bleckers/brtro-420-better-blazin/brtro-reflow/splash-chm.h

#define splash_width 128
#define splash_height 64
static const uint8_t splash_bits[] U8X8_PROGMEM  = {
   0xff, 0xff, 0xff, 0xff, 0xff, 0xff, 0xff, 0xff, 0xff, 0xff, 0xff, 0xff,
   0xff, 0xff, 0xff, 0xff, 0x01, 0x00, 0x00, 0x00, 0x00, 0x00, 0x00, 0x00,
   0x00, 0x00, 0x00, 0x00, 0x00, 0x00, 0x00, 0x80, 0xfd, 0xff, 0xff, 0xff,
   0xff, 0xff, 0xff, 0xff, 0xff, 0xff, 0xff, 0xff, 0xff, 0xff, 0xff, 0xbf,
   0x05, 0x00, 0x00, 0x00, 0x00, 0x00, 0x00, 0x00, 0x00, 0x00, 0x00, 0x00,
   0x00, 0x00, 0x00, 0xa0, 0x05, 0x00, 0x00, 0x00, 0x00, 0x00, 0x00, 0x00,
   0x00, 0x00, 0x00, 0x00, 0x00, 0x00, 0x00, 0xa0, 0x05, 0x00, 0x00, 0x00,
   0x00, 0x00, 0x00, 0x00, 0x00, 0x78, 0x00, 0xf0, 0x00, 0xe0, 0x01, 0xa0,
   0x05, 0x00, 0x00, 0x00, 0x00, 0x00, 0x00, 0x00, 0x00, 0x88, 0x01, 0x10,
   0x03, 0x20, 0x06, 0xa0, 0x05, 0x00, 0x00, 0x00, 0x00, 0x00, 0x00, 0x00,
   0x00, 0x08, 0x02, 0x10, 0x04, 0x20, 0x08, 0xa0, 0x85, 0x20, 0x08, 0x20,
   0x00, 0x00, 0x00, 0x00, 0x00, 0x38, 0x04, 0x70, 0x08, 0xe0, 0x10, 0xa0,
   0x85, 0x20, 0x08, 0x20, 0x00, 0x00, 0x00, 0x00, 0x00, 0xc4, 0x08, 0x88,
   0x11, 0x10, 0x23, 0xa0, 0x85, 0x20, 0x08, 0x20, 0x00, 0x00, 0x00, 0x00,
   0x00, 0x64, 0x11, 0x38, 0x22, 0x90, 0x45, 0xa0, 0x05, 0x51, 0xc4, 0x23,
   0x1c, 0x1c, 0x9a, 0xe1, 0x01, 0x94, 0x22, 0x48, 0x44, 0x50, 0x8a, 0xa0,
   0x05, 0x51, 0x24, 0x24, 0x22, 0x22, 0x66, 0x12, 0x02, 0x94, 0x44, 0x48,
   0x88, 0x50, 0x12, 0xa1, 0x05, 0x51, 0x24, 0x24, 0x01, 0x41, 0x22, 0x12,
   0x02, 0x62, 0x48, 0x34, 0x96, 0x88, 0x21, 0xa1, 0x05, 0x8a, 0xe2, 0x27,
   0x01, 0x41, 0x22, 0xf2, 0x03, 0x02, 0x88, 0x04, 0x19, 0x09, 0x20, 0xa2,
   0x05, 0x8a, 0x22, 0x20, 0x01, 0x41, 0x22, 0x12, 0x00, 0x06, 0x93, 0x04,
   0x29, 0x19, 0x4c, 0xa2, 0x05, 0x8a, 0x22, 0x20, 0x01, 0x41, 0x22, 0x12,
   0x00, 0x8a, 0x94, 0x04, 0x26, 0x29, 0x52, 0xa2, 0x05, 0x04, 0x21, 0x24,
   0x22, 0x22, 0x22, 0x12, 0x02, 0x89, 0xf4, 0x32, 0xe0, 0x25, 0xd2, 0xa3,
   0x05, 0x04, 0xc1, 0x23, 0x1c, 0x1c, 0x22, 0xe2, 0x01, 0x07, 0x0f, 0x4a,
   0x1e, 0x1c, 0x3c, 0xa0, 0x05, 0x00, 0x00, 0x00, 0x00, 0x00, 0x00, 0x00,
   0x00, 0xf1, 0x00, 0xea, 0x01, 0xc4, 0x03, 0xa0, 0x05, 0x00, 0x00, 0x00,
   0x00, 0x00, 0x00, 0x00, 0x00, 0x0f, 0x00, 0x1e, 0x00, 0x3c, 0x00, 0xa0,
   0x05, 0x00, 0x00, 0x00, 0x00, 0x00, 0x00, 0x00, 0x00, 0x00, 0x00, 0x00,
   0x00, 0x00, 0x00, 0xa0, 0x05, 0x00, 0x00, 0x00, 0x00, 0x00, 0x00, 0x00,
   0x00, 0x00, 0x00, 0x00, 0x00, 0x00, 0x00, 0xa0, 0xfd, 0xff, 0xff, 0xff,
   0xff, 0xff, 0xff, 0xff, 0xff, 0xff, 0xff, 0xff, 0xff, 0xff, 0xff, 0xbf,
   0xfd, 0xff, 0xff, 0xff, 0xff, 0xff, 0xff, 0xff, 0xff, 0xff, 0xff, 0xff,
   0xff, 0xff, 0xff, 0xbf, 0xfd, 0xff, 0xff, 0xff, 0xff, 0xff, 0xff, 0xff,
   0xff, 0xff, 0xff, 0xff, 0xff, 0xff, 0xff, 0xbf, 0xfd, 0xff, 0x87, 0xf7,
   0xb7, 0xbf, 0x01, 0x7f, 0xf0, 0xff, 0xff, 0x7c, 0xf8, 0xe1, 0xff, 0xbf,
   0xfd, 0xff, 0x7b, 0xf7, 0x37, 0x9f, 0xfd, 0xbe, 0xef, 0xff, 0x7f, 0xbd,
   0xf7, 0xde, 0xff, 0xbf, 0xfd, 0xff, 0xfd, 0xf6, 0xb7, 0xae, 0xfd, 0xdd,
   0xdf, 0xff, 0x7f, 0xdd, 0x6f, 0xbf, 0xff, 0xbf, 0xfd, 0xff, 0xfd, 0xf7,
   0xb7, 0xb5, 0xfd, 0xdd, 0xdf, 0xff, 0xbf, 0xdd, 0x6f, 0xbf, 0xff, 0xbf,
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
