bleckers/brtro-420-better-blazin/brtro-reflow/history_buffer.h

/**
   MappyDot Firmware - history_buffer.h

   Copyright (C) 2017 SensorDots.org

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
*/


#ifndef BUFFER_H_
#define BUFFER_H_

#ifdef __cplusplus
extern "C" {
#endif

#include <stddef.h>
#include <stdint.h>


typedef struct circular_history_buffer
{
    void *buffer;     // data buffer
    void *buffer_end; // end of data buffer
    size_t capacity;  // maximum number of items in the buffer
    size_t count;     // number of items in the buffer
    size_t sz;        // size of each item in the buffer
    void *head;       // pointer to head
    void *tail;       // pointer to tail
} circular_history_buffer;

void hb_init(circular_history_buffer *cb, size_t capacity, size_t sz);

void hb_free(circular_history_buffer *cb);

void hb_push_back(circular_history_buffer *cb, const void *item);

void hb_pop_front(circular_history_buffer *cb, void *item);

void hb_straighten(circular_history_buffer *hb, int16_t *straightened, size_t count);

#ifdef __cplusplus
} // extern "C"
#endif

#endif /* BUFFER_H_ */
